fuyarovh/organ/3d_printed_parts/3mf/pedalboard/pedals/s_18x_Pedal Back white.3mf

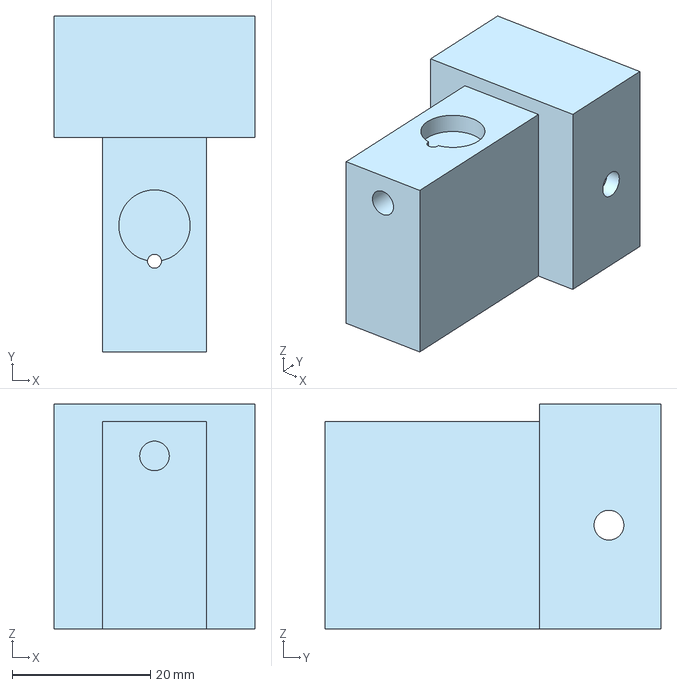
[picture p17: CAD file, 2026-01-05]
3d_printed_parts/3mf/pedalboard/pedals/s_18x_Pedal Back white.3mf
29.0 x 48.5 x 32.5 mm
