fuyarovh/organ/3d_printed_parts/3mf/top/din_rail_attachments/1x_power_switch.3mf

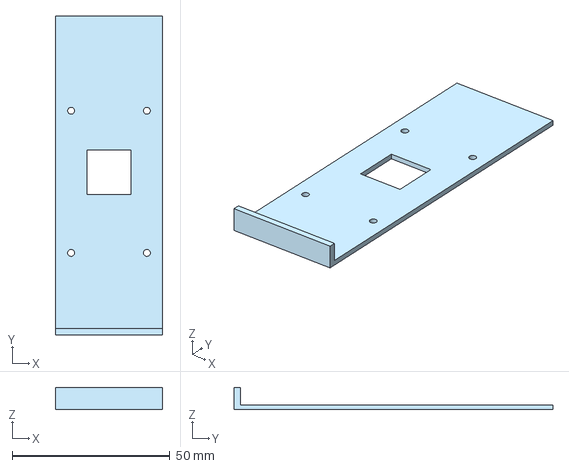
[picture p19: CAD file, 2026-01-05]
3d_printed_parts/3mf/top/din_rail_attachments/1x_power_switch.3mf
34.0 x 101.0 x 7.00 mm
