fuyarovh/organ/3d_printed_parts/3mf/top/standoffs/1x_Standoff_closed.3mf

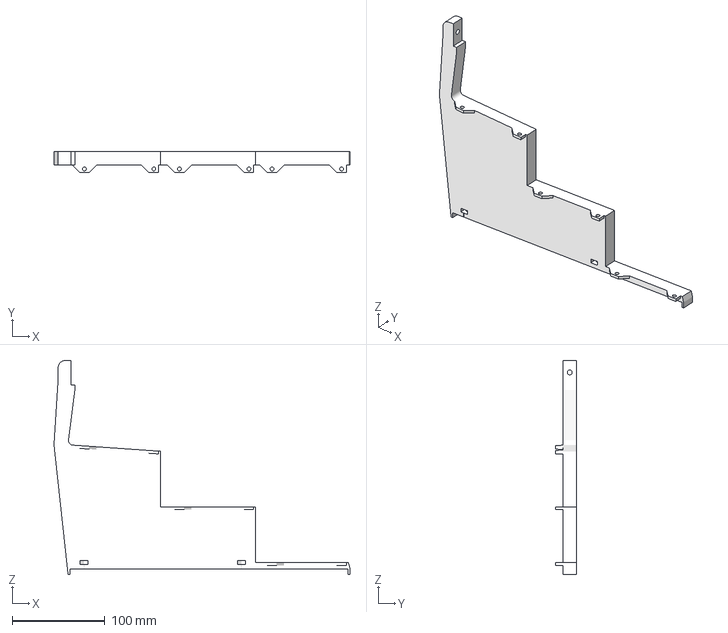
[picture p20: CAD file, 2026-01-05]
3d_printed_parts/3mf/top/standoffs/1x_Standoff_closed.3mf
319.2 x 23.0 x 231.0 mm
