fuyarovh/organ/3d_printed_parts/3mf/pedalboard/pedals/12x_Pedal Front black.3mf

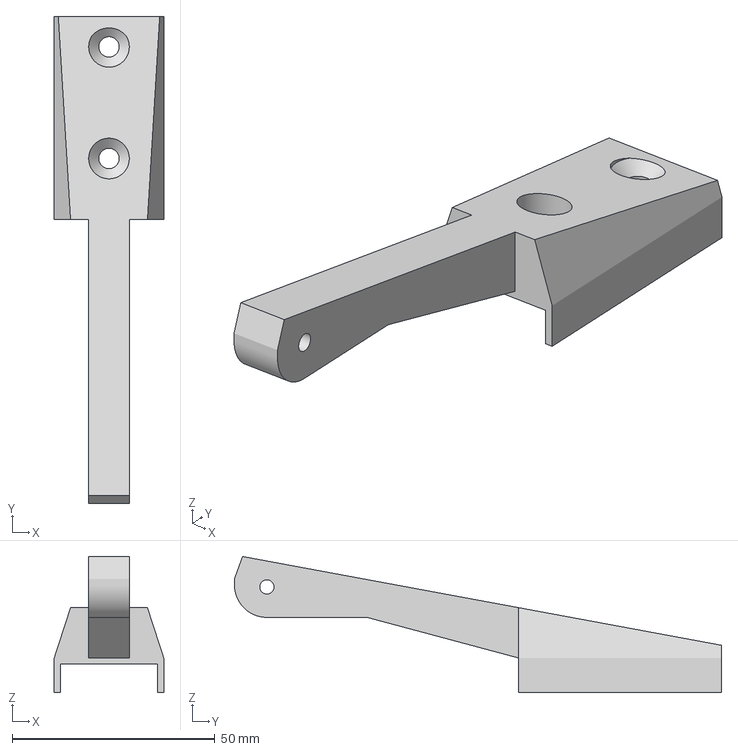
[picture p22: CAD file, 2026-01-05]
3d_printed_parts/3mf/pedalboard/pedals/12x_Pedal Front black.3mf
27.0 x 120.0 x 33.5 mm
