fuyarovh/organ/3d_printed_parts/3mf/pedalboard/pedals/black keys/1x_Black key C#3.3mf

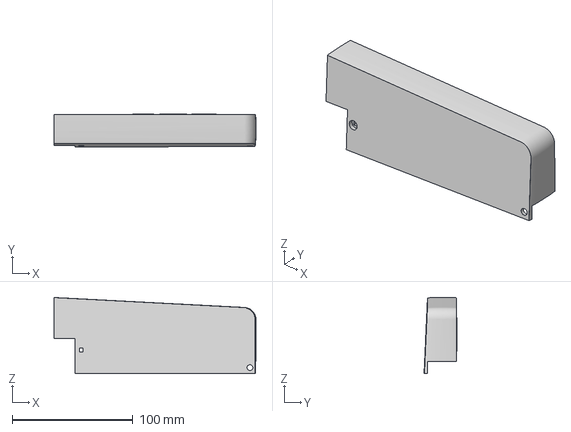
[picture p23: CAD file, 2026-01-05]
3d_printed_parts/3mf/pedalboard/pedals/black keys/1x_Black key C#3.3mf
167.1 x 27.3 x 62.9 mm
