fuyarovh/organ/3d_printed_parts/3mf/top/2x_keyboard_stand_adapter.3mf

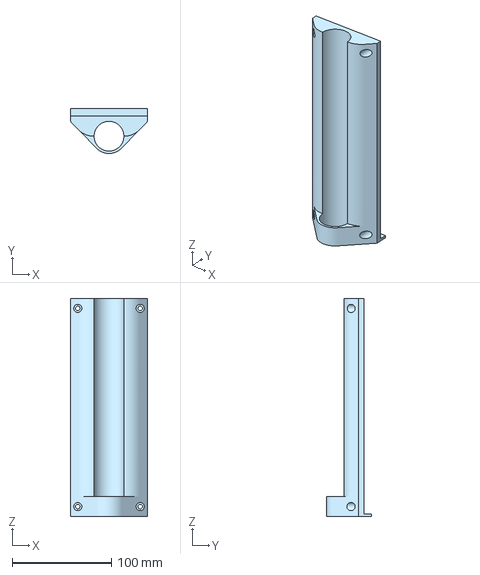
[picture p24: CAD file, 2026-01-05]
3d_printed_parts/3mf/top/2x_keyboard_stand_adapter.3mf
78.0 x 45.5 x 220.0 mm
