fuyarovh/organ/3d_printed_parts/3mf/top/din_rail_attachments/0x_din_rail_expansion.3mf

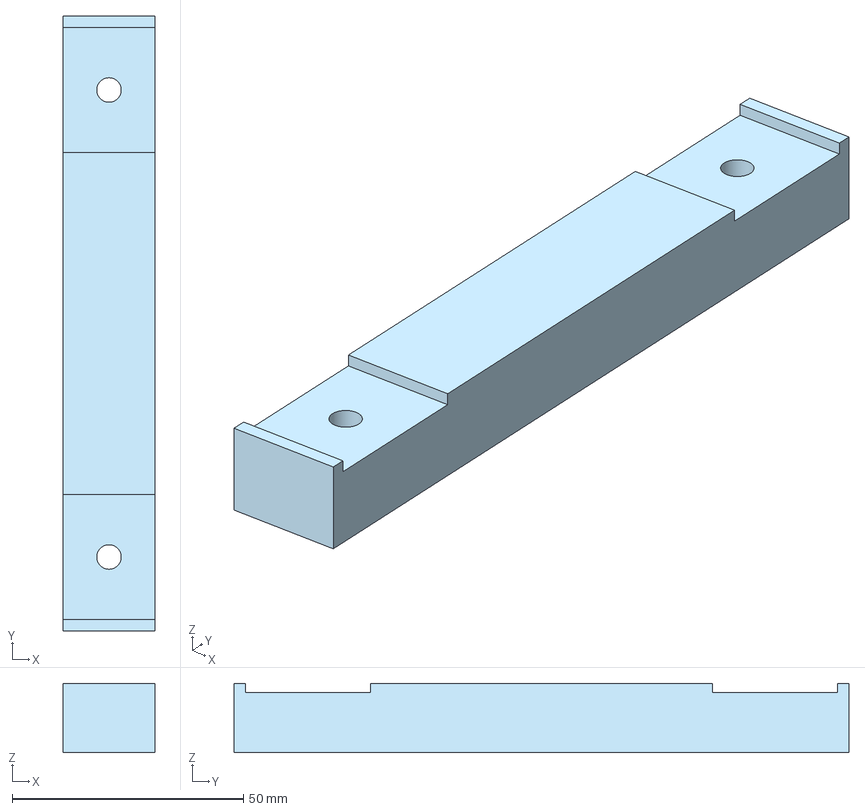
[picture p25: CAD file, 2026-01-05]
3d_printed_parts/3mf/top/din_rail_attachments/0x_din_rail_expansion.3mf
20.0 x 133.0 x 15.0 mm
