fuyarovh/organ/3d_printed_parts/3mf/pedalboard/s_1x_pedal back right right.3mf

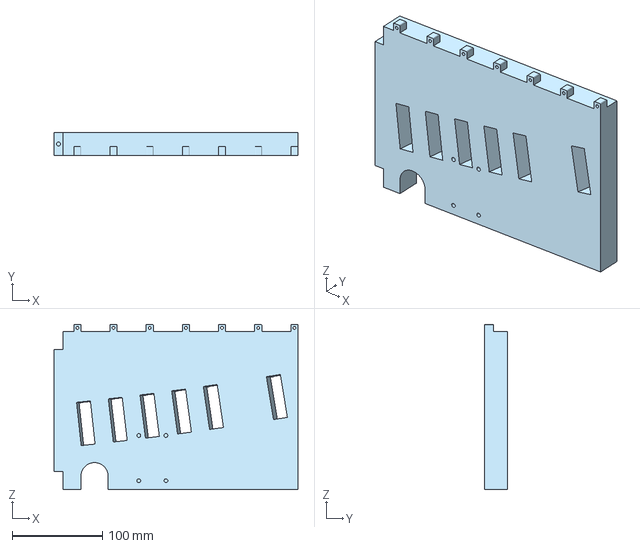
[picture p26: CAD file, 2026-01-05]
3d_printed_parts/3mf/pedalboard/s_1x_pedal back right right.3mf
269.8 x 25.0 x 183.0 mm
