fuyarovh/organ/3d_printed_parts/3mf/pedalboard/1x_pedal front left left.3mf

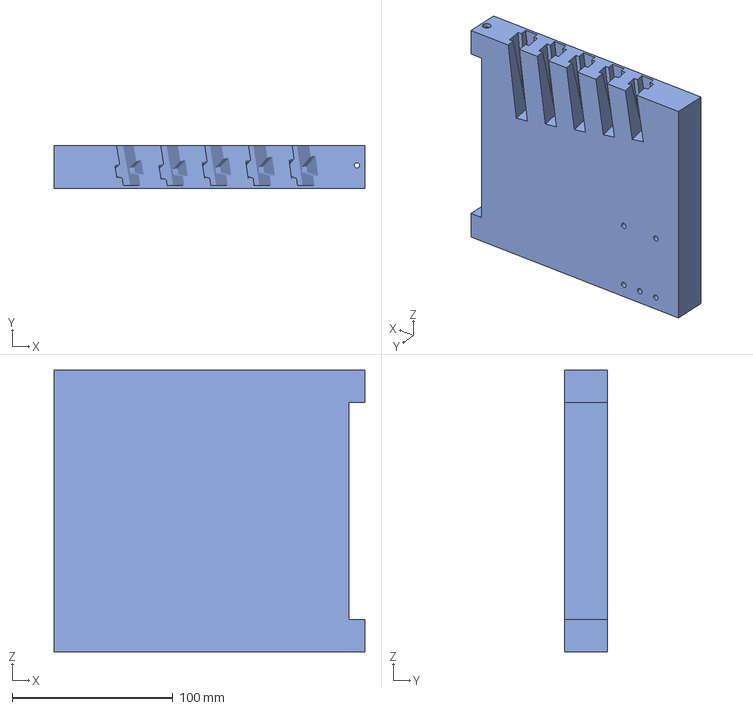
[picture p27: CAD file, 2026-01-05]
3d_printed_parts/3mf/pedalboard/1x_pedal front left left.3mf
193.3 x 27.0 x 175.0 mm
