fuyarovh/organ/3d_printed_parts/3mf/pedalboard/pedals/black keys/1x_Black key D#2.3mf

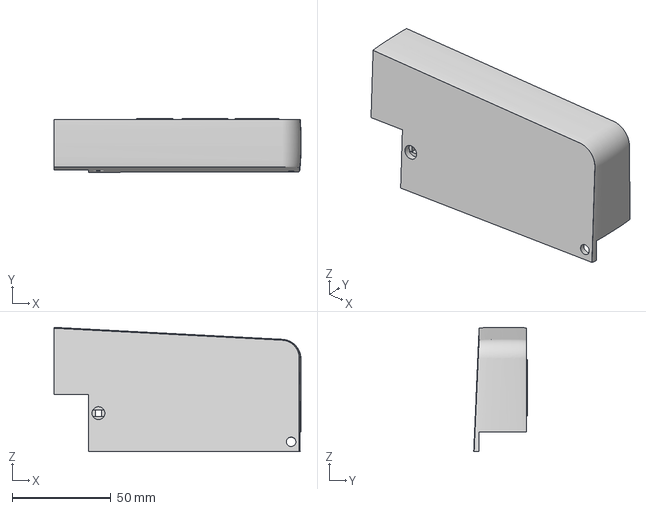
[picture p28: CAD file, 2026-01-05]
3d_printed_parts/3mf/pedalboard/pedals/black keys/1x_Black key D#2.3mf
125.0 x 27.1 x 62.9 mm
