fuyarovh/organ/3d_printed_parts/3mf/top/1x_1xM_audio_interface_mount_front.3mf

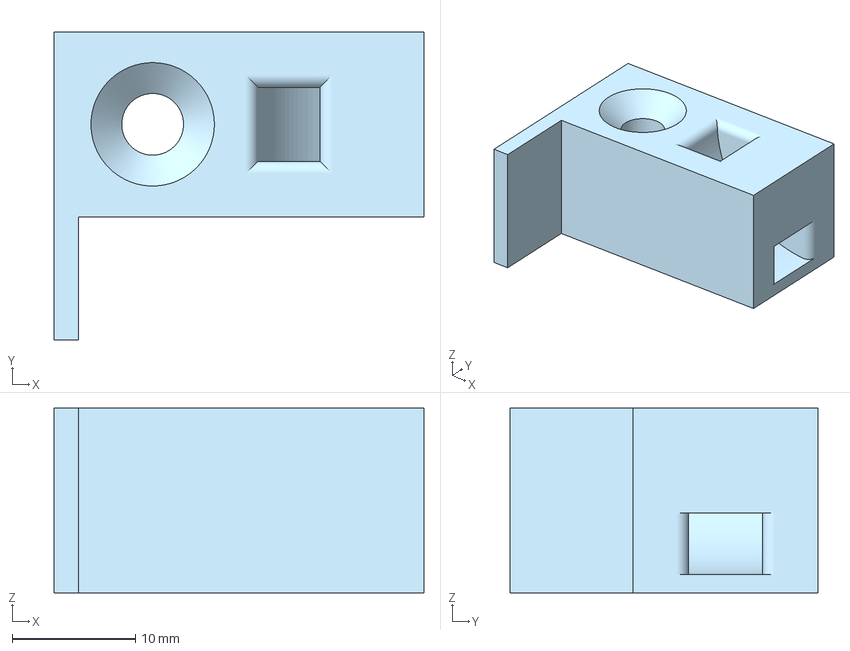
[picture p29: CAD file, 2026-01-05]
3d_printed_parts/3mf/top/1x_1xM_audio_interface_mount_front.3mf
30.0 x 25.0 x 15.0 mm
