fuyarovh/organ/3d_printed_parts/3mf/pedalboard/0x_pedal back left middle cover.3mf

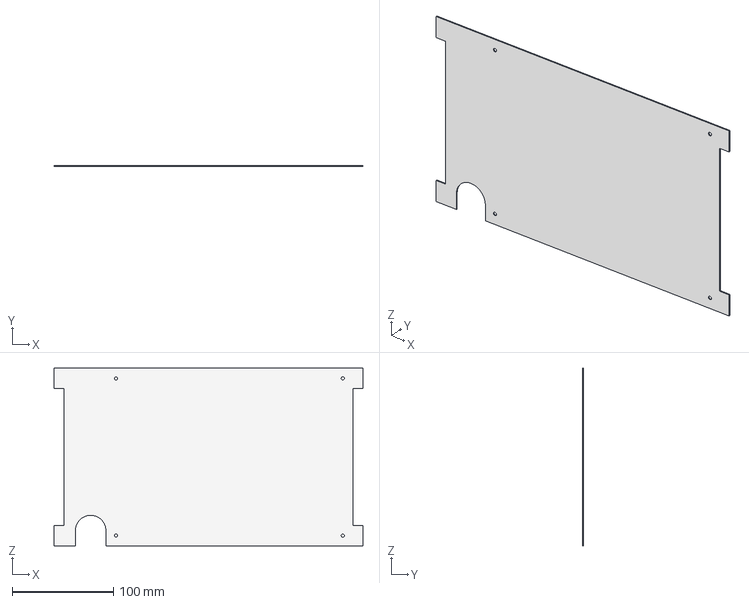
[picture p30: CAD file, 2026-01-05]
3d_printed_parts/3mf/pedalboard/0x_pedal back left middle cover.3mf
304.5 x 1.00 x 175.0 mm
