fuyarovh/organ/3d_printed_parts/3mf/pedalboard/pedals/black keys/1x_Black key F#1.3mf

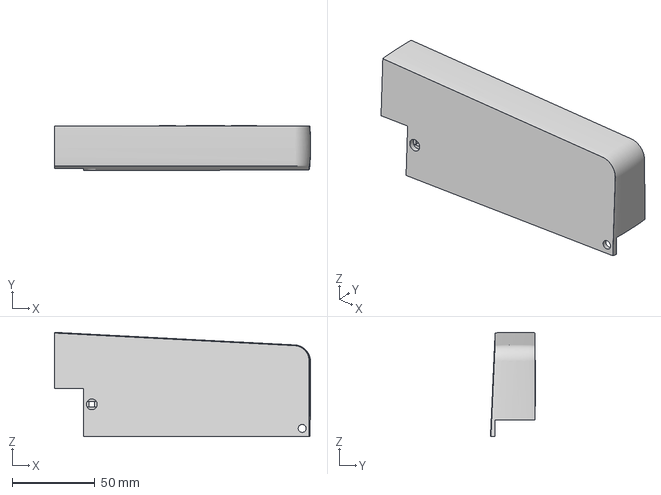
[picture p31: CAD file, 2026-01-05]
3d_printed_parts/3mf/pedalboard/pedals/black keys/1x_Black key F#1.3mf
154.4 x 27.2 x 62.9 mm
