fuyarovh/organ/3d_printed_parts/3mf/top/1x_setter_right.3mf

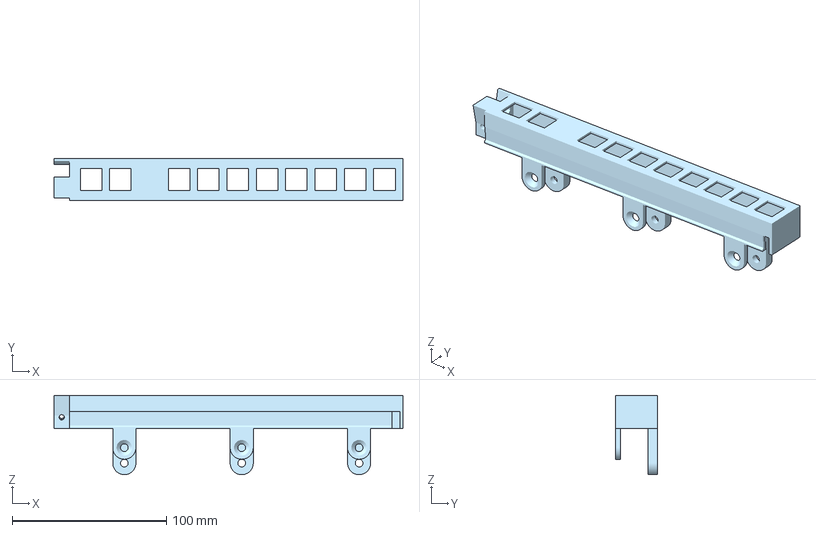
[picture p32: CAD file, 2026-01-05]
3d_printed_parts/3mf/top/1x_setter_right.3mf
226.6 x 27.2 x 51.5 mm
