fuyarovh/organ/3d_printed_parts/3mf/pedalboard/pedals/black keys/1x_Black key F#2.3mf

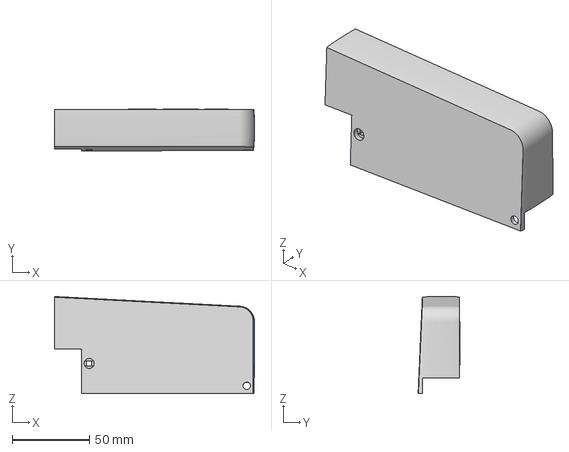
[picture p33: CAD file, 2026-01-05]
3d_printed_parts/3mf/pedalboard/pedals/black keys/1x_Black key F#2.3mf
129.7 x 27.2 x 62.9 mm
