fuyarovh/organ/3d_printed_parts/3mf/pedalboard/s_1x_pedal back left left.3mf

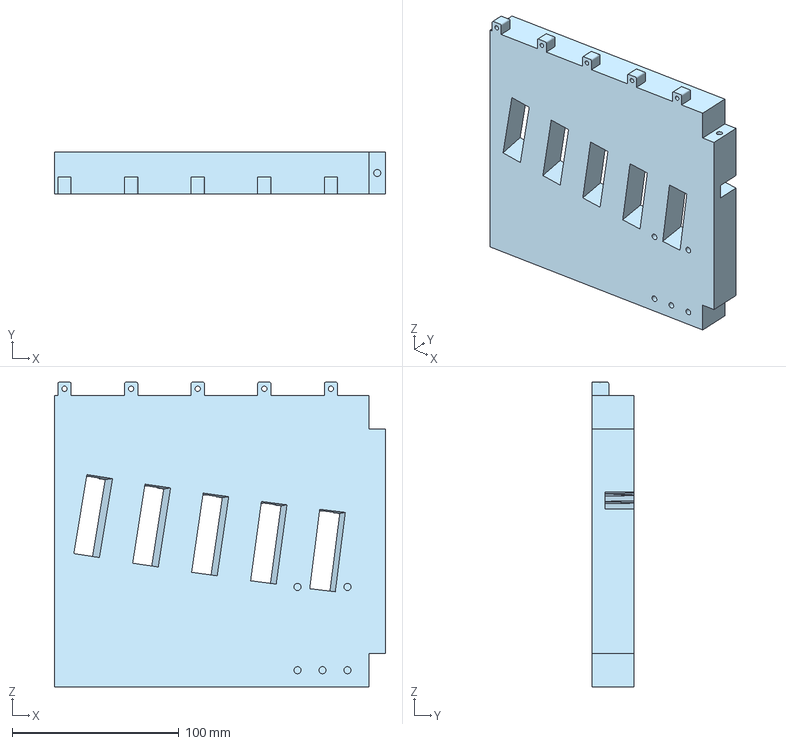
[picture p34: CAD file, 2026-01-05]
3d_printed_parts/3mf/pedalboard/s_1x_pedal back left left.3mf
198.8 x 25.0 x 183.0 mm
