fuyarovh/organ/3d_printed_parts/3mf/pedalboard/s_1x_pedal back left right.3mf

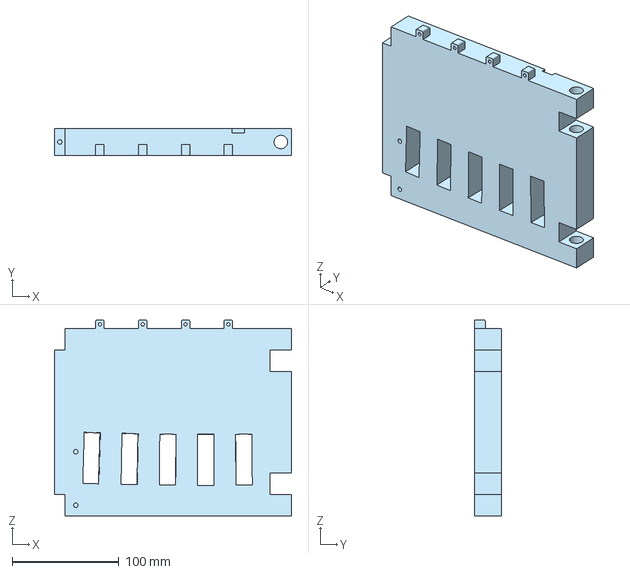
[picture p36: CAD file, 2026-01-05]
3d_printed_parts/3mf/pedalboard/s_1x_pedal back left right.3mf
221.5 x 25.0 x 183.0 mm
