fuyarovh/organ/3d_printed_parts/3mf/pedalboard/0x_pedal back left left cover.3mf

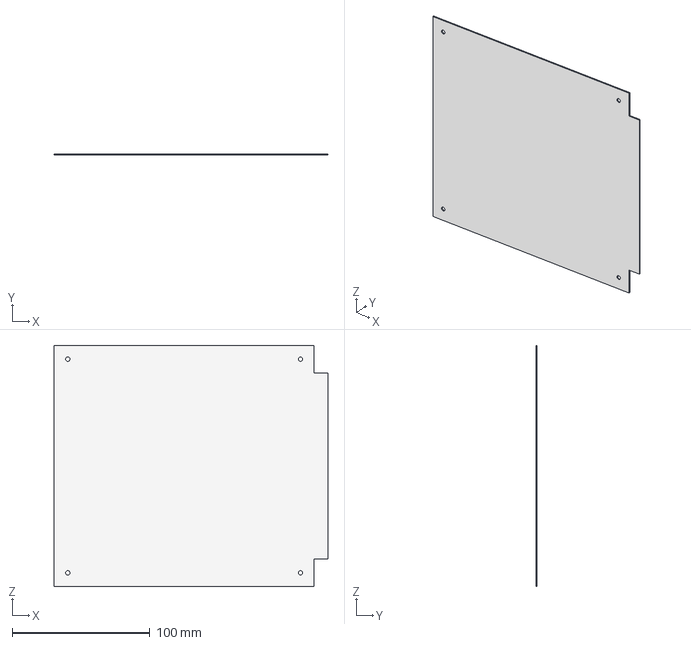
[picture p37: CAD file, 2026-01-05]
3d_printed_parts/3mf/pedalboard/0x_pedal back left left cover.3mf
198.8 x 1.00 x 175.0 mm
