fuyarovh/organ/3d_printed_parts/step/Front Back Connector.step

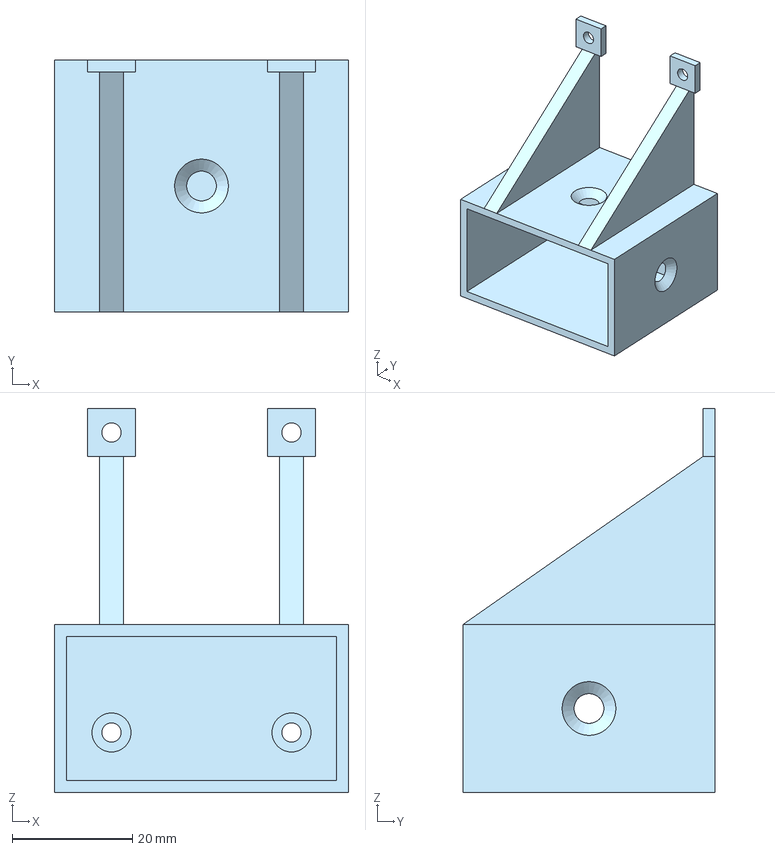
[picture p38: CAD file, 2026-01-05]
3d_printed_parts/step/Front Back Connector.step
49.0 x 42.0 x 64.0 mm
