fuyarovh/organ/3d_printed_parts/3mf/pedalboard/1x_pedal front right right.3mf

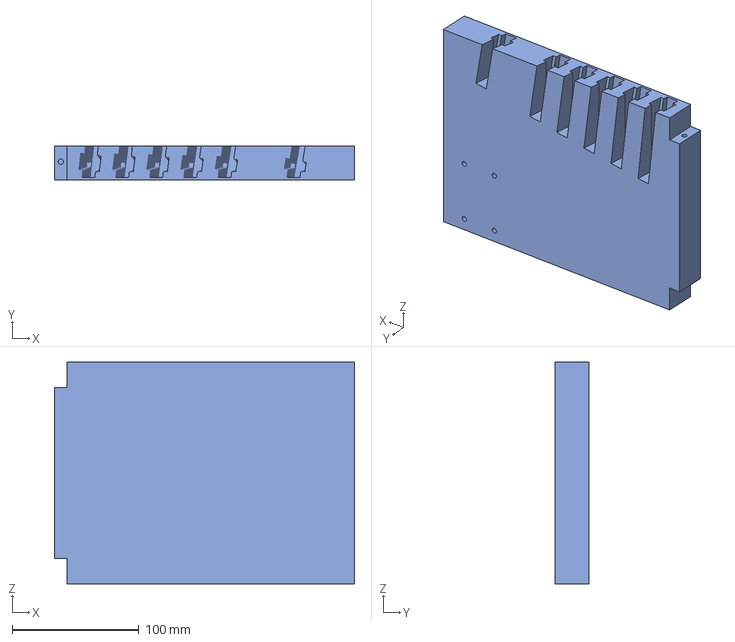
[picture p39: CAD file, 2026-01-05]
3d_printed_parts/3mf/pedalboard/1x_pedal front right right.3mf
236.7 x 27.0 x 175.0 mm
