fuyarovh/organ/3d_printed_parts/3mf/pedalboard/1x_pedal front left middle.3mf

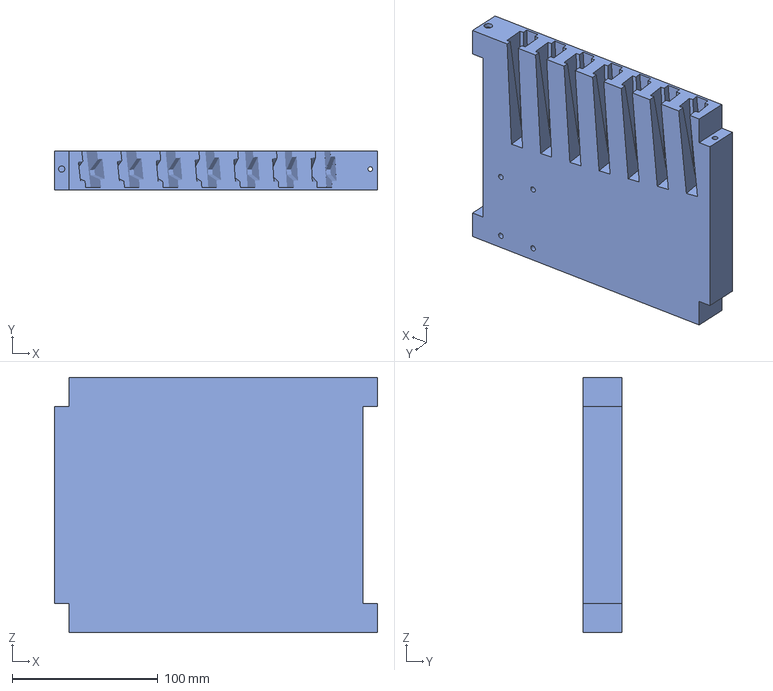
[picture p40: CAD file, 2026-01-05]
3d_printed_parts/3mf/pedalboard/1x_pedal front left middle.3mf
221.6 x 27.0 x 175.0 mm
