fuyarovh/organ/3d_printed_parts/3mf/pedalboard/1x_pedal front left right.3mf

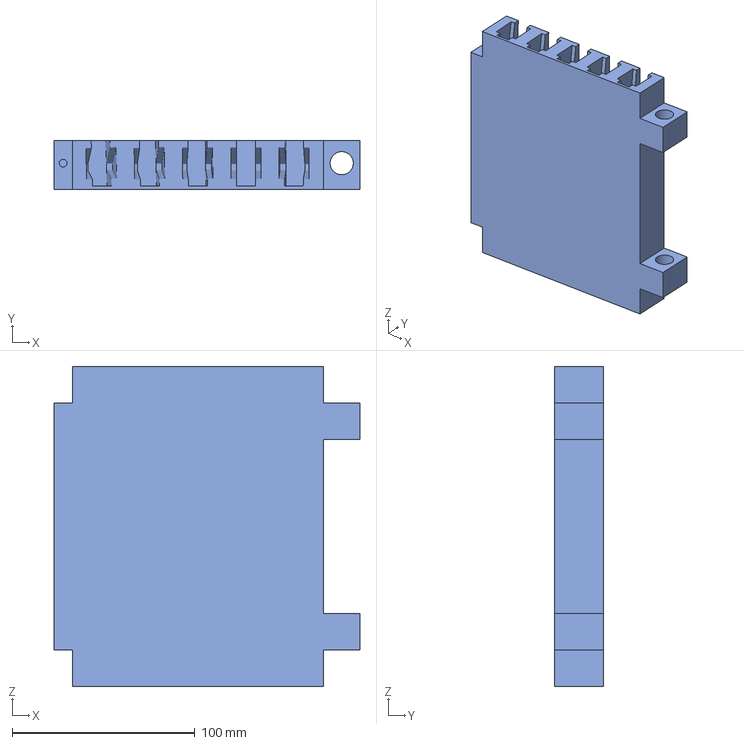
[picture p41: CAD file, 2026-01-05]
3d_printed_parts/3mf/pedalboard/1x_pedal front left right.3mf
167.3 x 27.0 x 175.0 mm
