fuyarovh/organ/3d_printed_parts/step/pedal front back frame.step

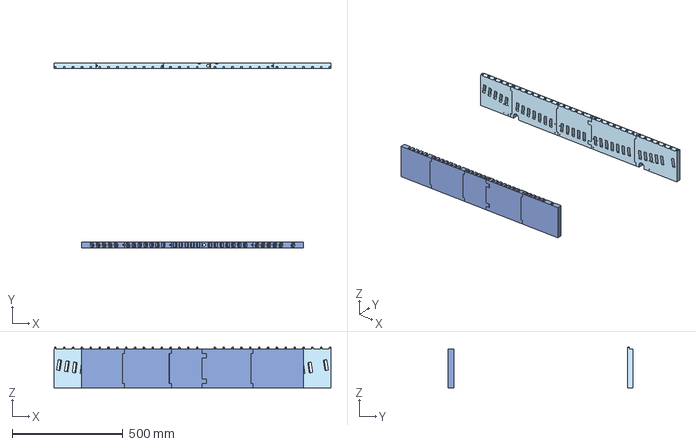
[picture p42: CAD file, 2026-01-05]
3d_printed_parts/step/pedal front back frame.step
1250.0 x 836.0 x 183.0 mm
